mafdezmoreno/MSP430G2-Alarm-Clock/clockTimer.cpp

#include "clockTimer.h"

clockTimer::clockTimer()
{
    initTimer0();
    upTimerOneSec();
}

void clockTimer::initTimer0()
{

    // Timer0_A Control Register
    TACTL |= TASSEL_1 + ID_3;
    // ID_3: Input divider by 8
    // TASSEL_1: Use ACLK as source for timer
    // ACLK == 32768Hz (Current clock source)
    // ACLK/8 = 4096Hz
}

void clockTimer::stopTimer0()
{
    // Timer_A Control Register
    TACTL |= MC_0;    // Stop mode
    TACCTL0 &= ~CCIE; // Disable Interrupts on Timer
}

void clockTimer::upTimerBuzz()
{
    stopTimer0();
    TACCR0 = 16; // callback every 3.9 ms (for buzzer)
    TACCTL0 |= CCIE;
    TACTL |= MC_1;   // Up mode: the timer counts up to TACCR0
}

void clockTimer::upTimerOneSec()
{
    stopTimer0();
    TACCR0 = 4096; // callback every 1 sec
    TACCTL0 |= CCIE;
    TACTL |= MC_1;   // Up mode: the timer counts up to TACCR0
}

void clockTimer::delay(unsigned msDelay)
{
    for (unsigned i = msDelay; i > 1; i--)
    {
            __delay_cycles( 1000 );
    }
}
