mafdezmoreno/MSP430G2-Alarm-Clock/BuzzerTimer.h

#ifndef BUZZERTIMER_H_
#define BUZZERTIMER_H_

class buzzerTimer
{
public:
    buzzerTimer();
    virtual ~buzzerTimer();

    //up_timer();
    //stop_timer();
    //init_timer();
};

#endif /* BUZZERTIMER_H_ */
